TomWhitwell/RadioMusic/Collateral/BuildImages/00.jpg

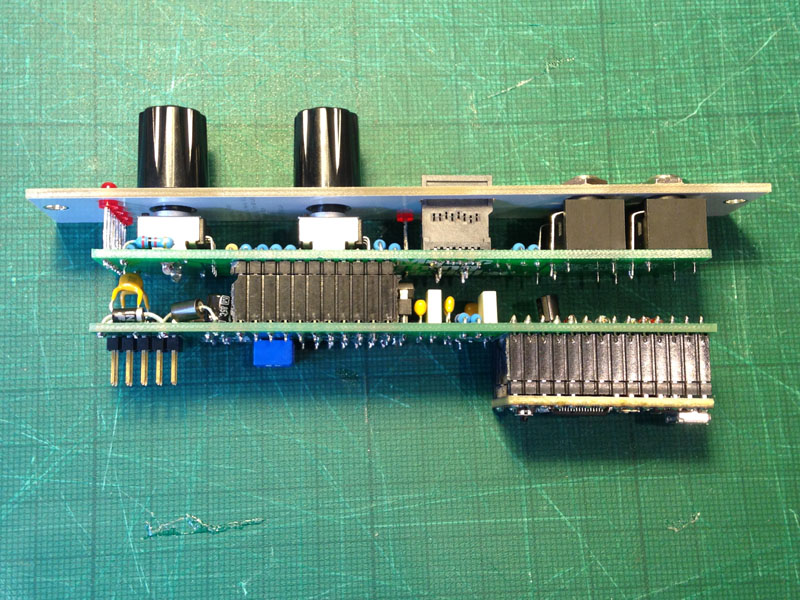
Collateral/BuildImages/00.jpg
