TomWhitwell/RadioMusic/Collateral/BuildImages/01.jpg

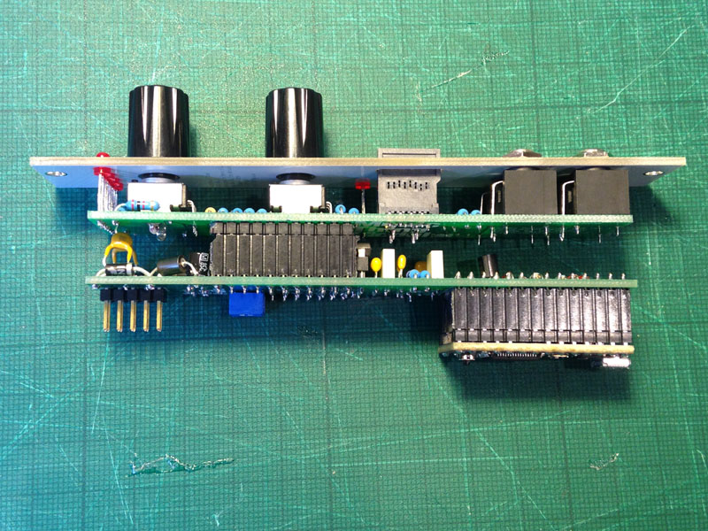
Collateral/BuildImages/01.jpg
