TomWhitwell/RadioMusic/Collateral/BuildImages/02.jpg

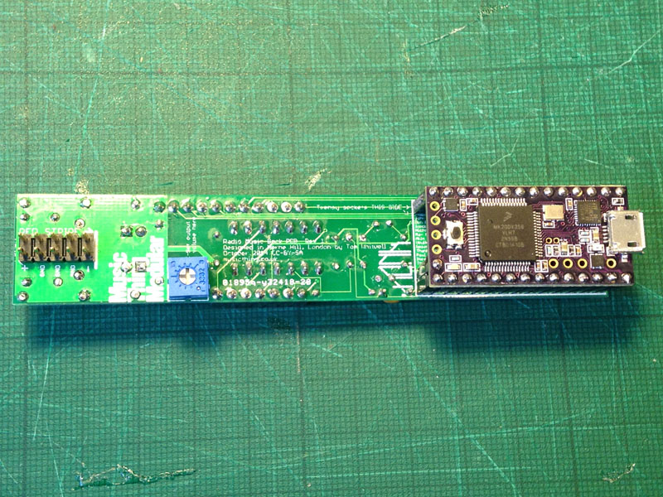
Collateral/BuildImages/02.jpg
