TomWhitwell/RadioMusic/Collateral/BuildImages/03.jpg

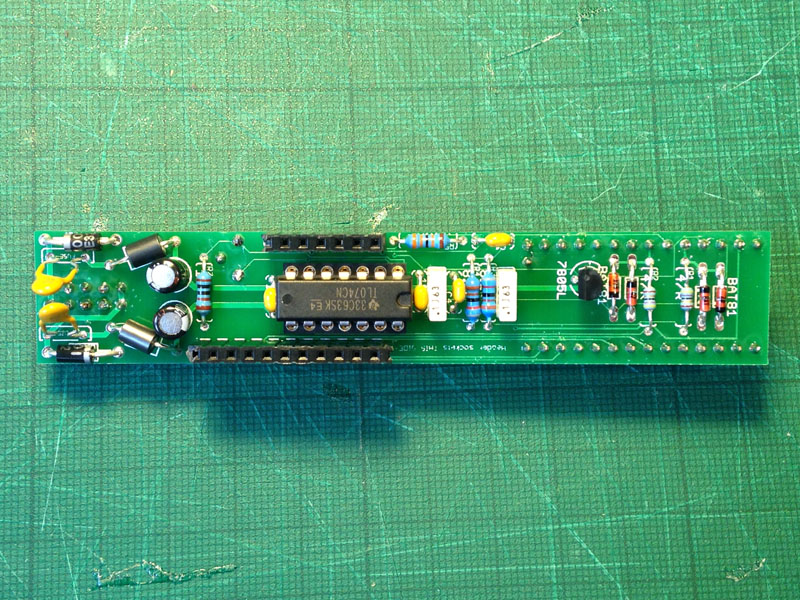
Collateral/BuildImages/03.jpg
