TomWhitwell/RadioMusic/Collateral/BuildImages/04.jpg

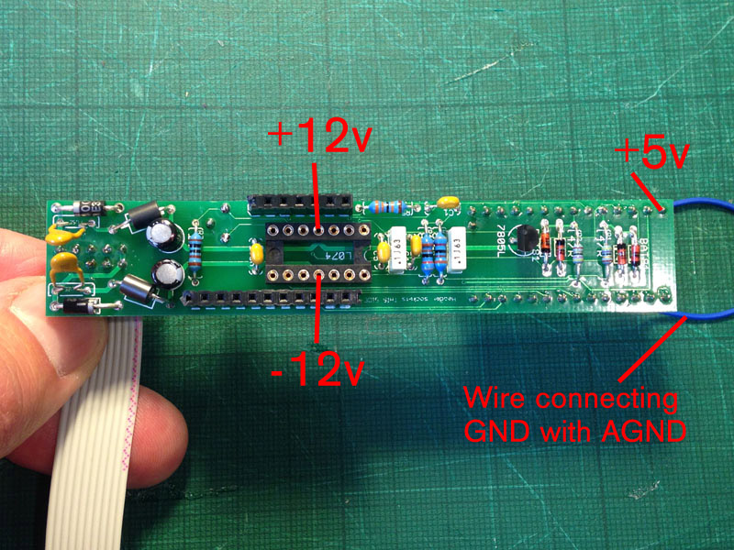
Collateral/BuildImages/04.jpg
