TomWhitwell/RadioMusic/Collateral/BuildImages/05.jpg

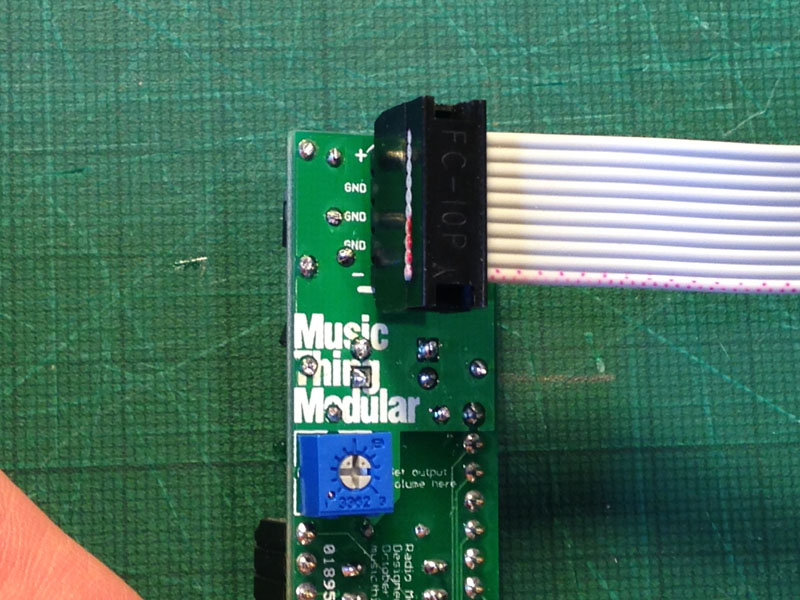
Collateral/BuildImages/05.jpg
