TomWhitwell/RadioMusic/Collateral/BuildImages/06.jpg

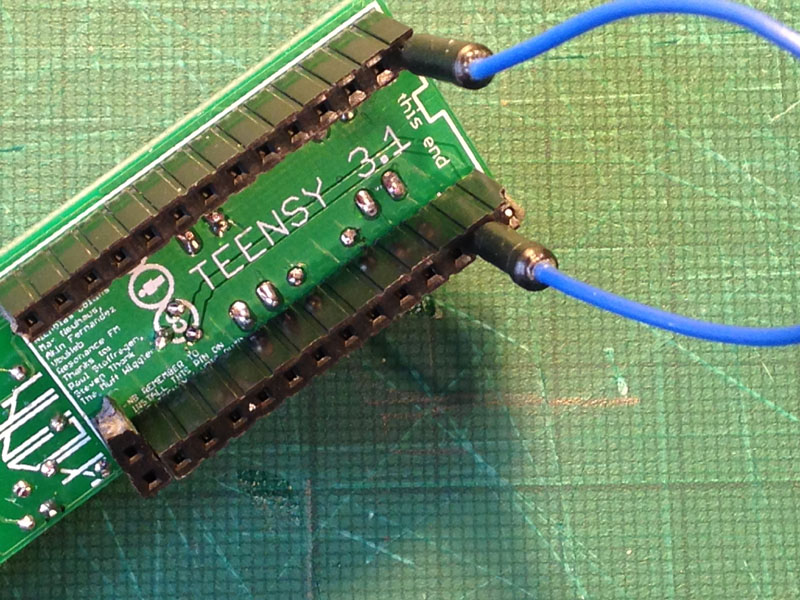
Collateral/BuildImages/06.jpg
