TomWhitwell/RadioMusic/Collateral/BuildImages/07.jpg

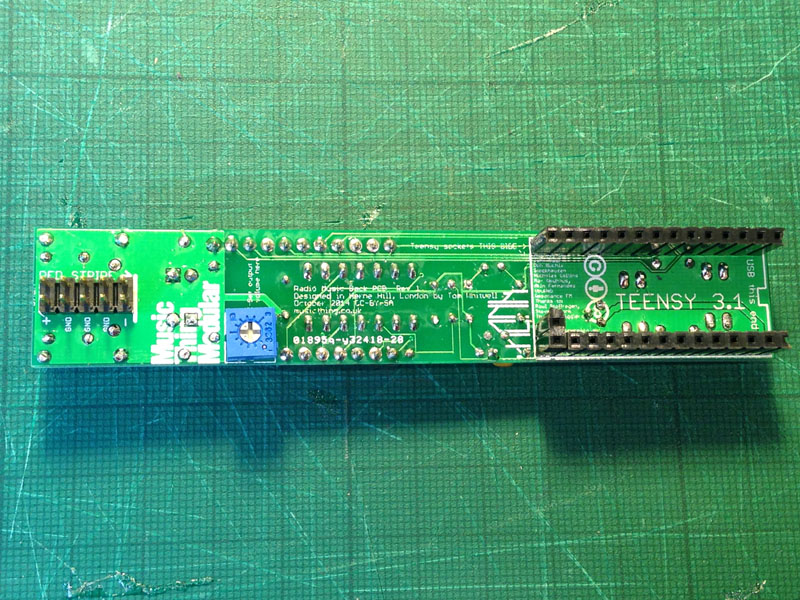
Collateral/BuildImages/07.jpg
