TomWhitwell/RadioMusic/Collateral/BuildImages/09.jpg

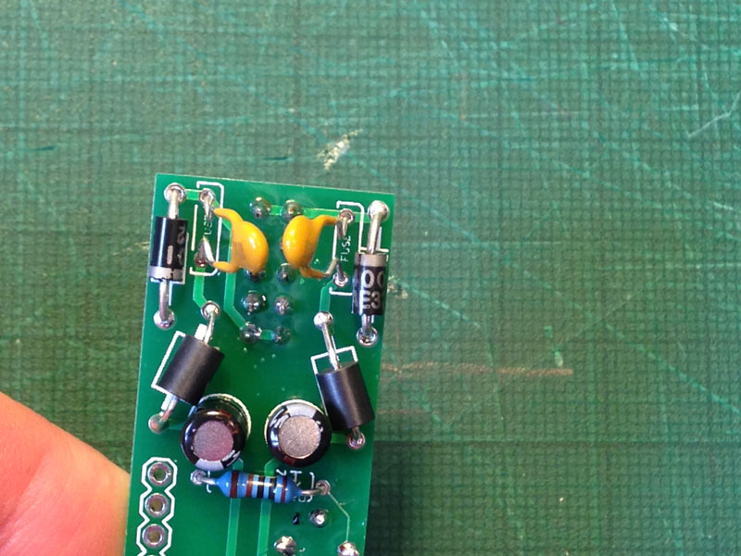
Collateral/BuildImages/09.jpg
