TomWhitwell/RadioMusic/Collateral/BuildImages/10.jpg

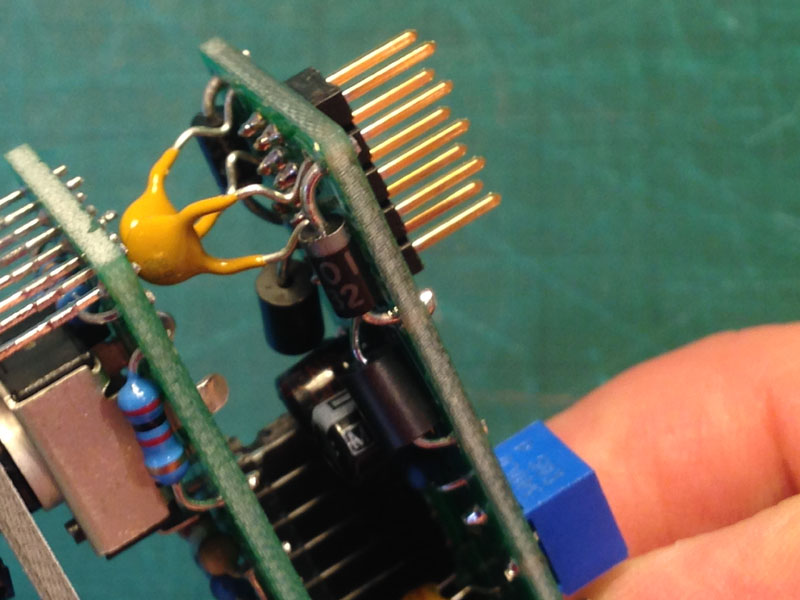
Collateral/BuildImages/10.jpg
