TomWhitwell/RadioMusic/Collateral/BuildImages/11.jpg

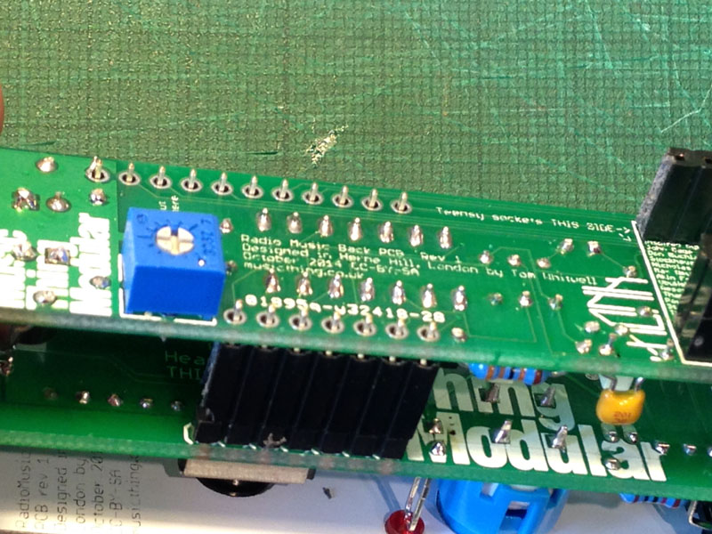
Collateral/BuildImages/11.jpg
