TomWhitwell/RadioMusic/Collateral/BuildImages/12.jpg

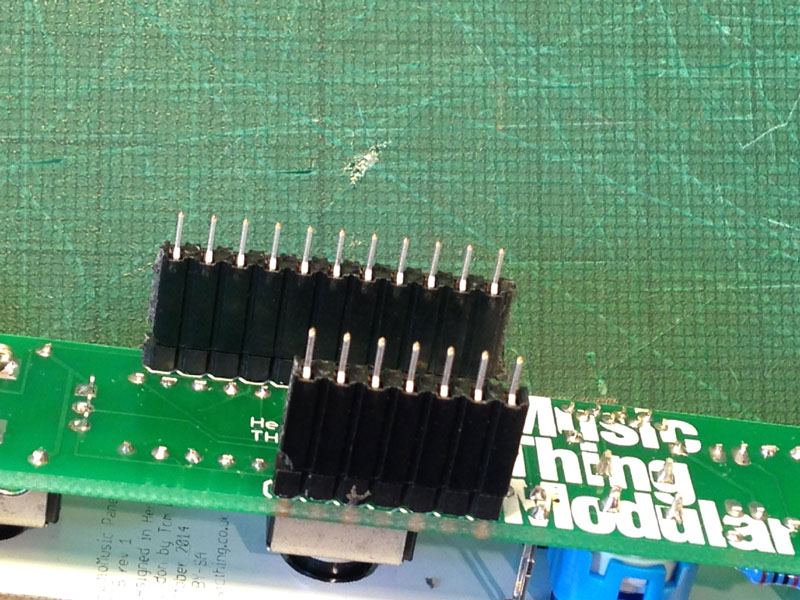
Collateral/BuildImages/12.jpg
