TomWhitwell/RadioMusic/Collateral/BuildImages/13.jpg

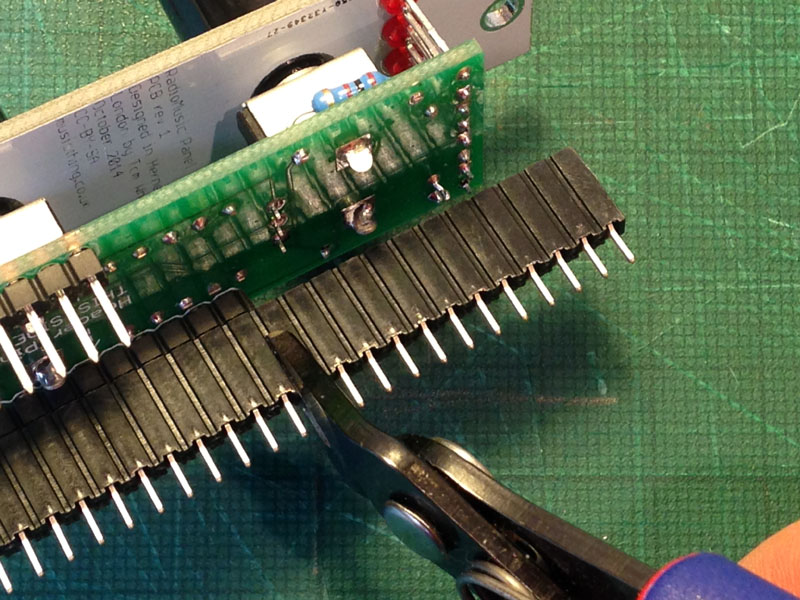
Collateral/BuildImages/13.jpg
