TomWhitwell/RadioMusic/Collateral/BuildImages/14.jpg

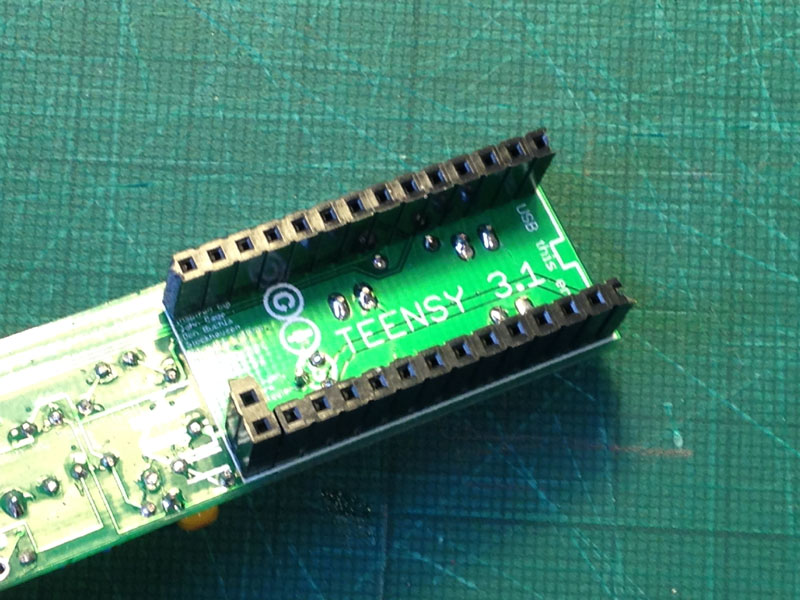
Collateral/BuildImages/14.jpg
