TomWhitwell/RadioMusic/Collateral/BuildImages/16.jpg

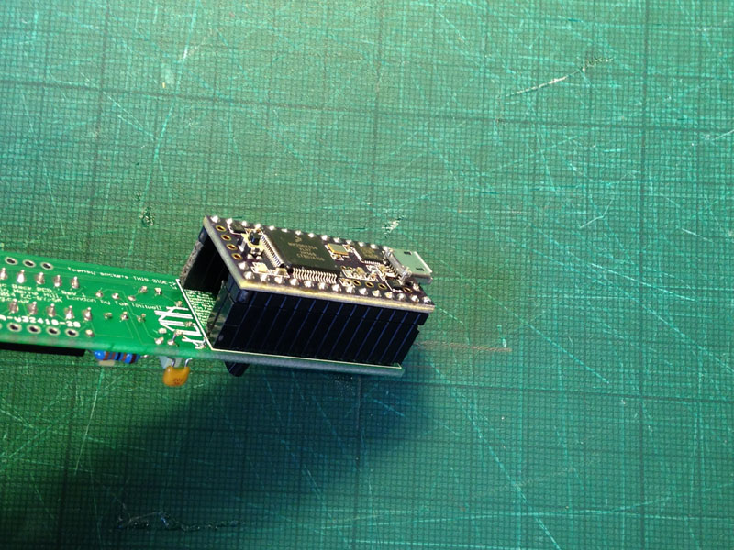
Collateral/BuildImages/16.jpg
