TomWhitwell/RadioMusic/Collateral/BuildImages/17.jpg

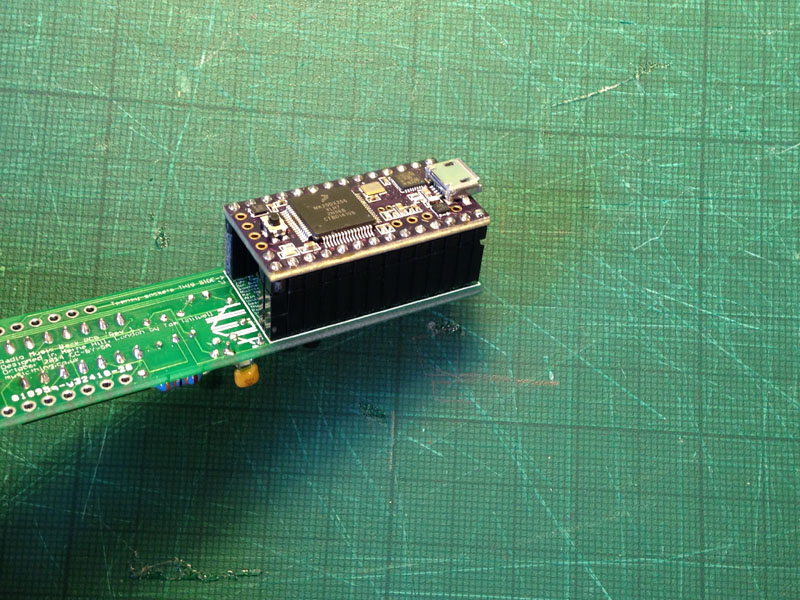
Collateral/BuildImages/17.jpg
