TomWhitwell/RadioMusic/Collateral/BuildImages/18.jpg

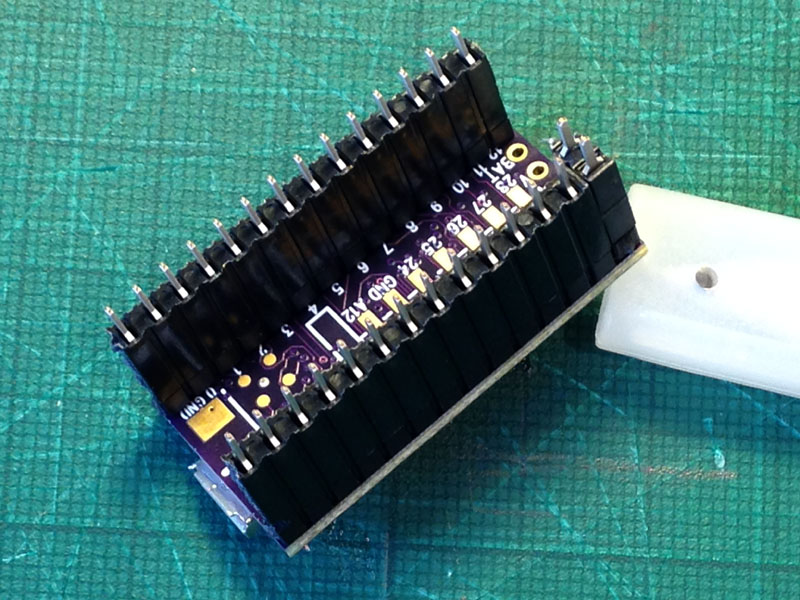
Collateral/BuildImages/18.jpg
