TomWhitwell/RadioMusic/Collateral/BuildImages/19.jpg

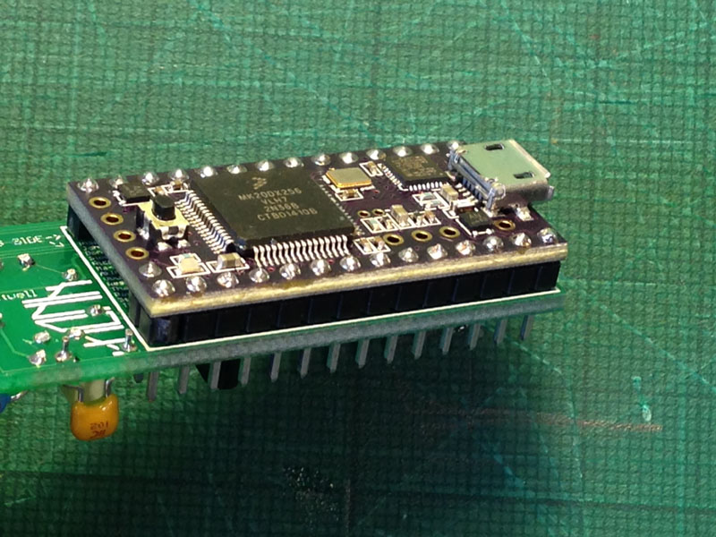
Collateral/BuildImages/19.jpg
