TomWhitwell/RadioMusic/Collateral/BuildImages/20.jpg

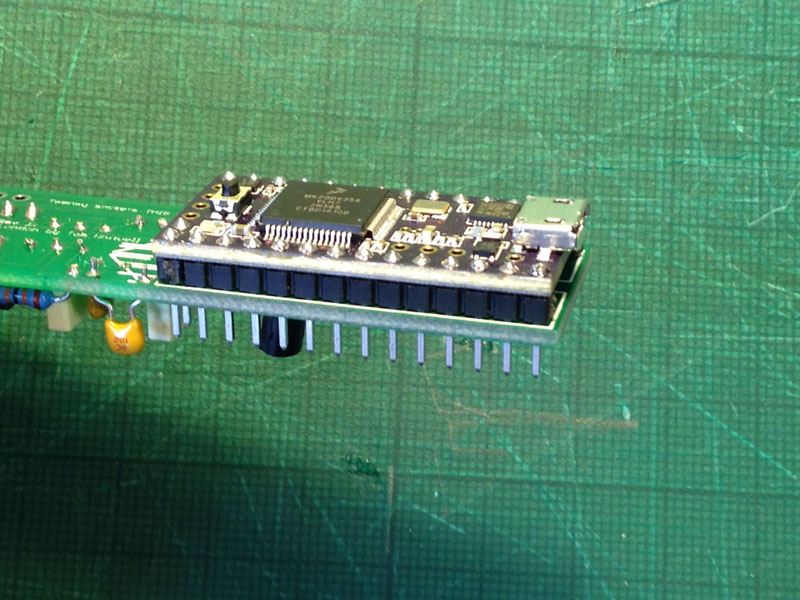
Collateral/BuildImages/20.jpg
