TomWhitwell/RadioMusic/Collateral/BuildImages/21.jpg

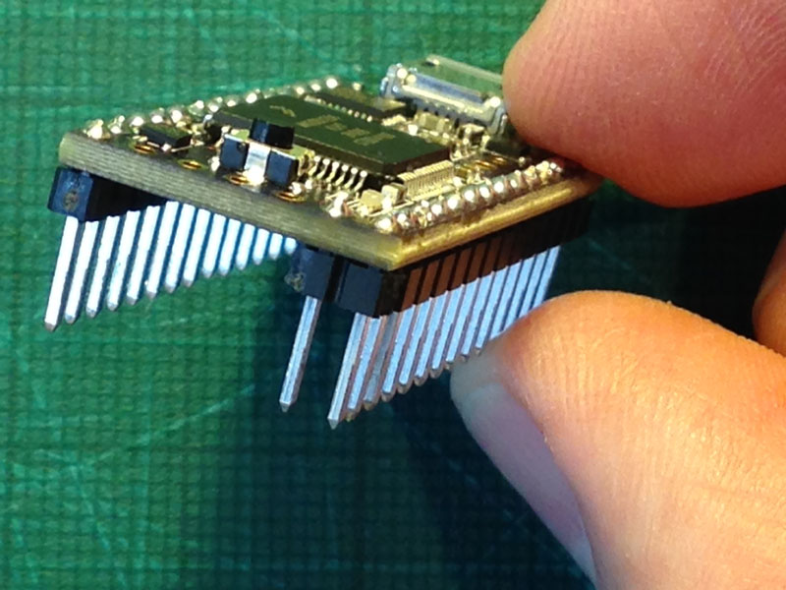
Collateral/BuildImages/21.jpg
