TomWhitwell/RadioMusic/Collateral/BuildImages/22.jpg

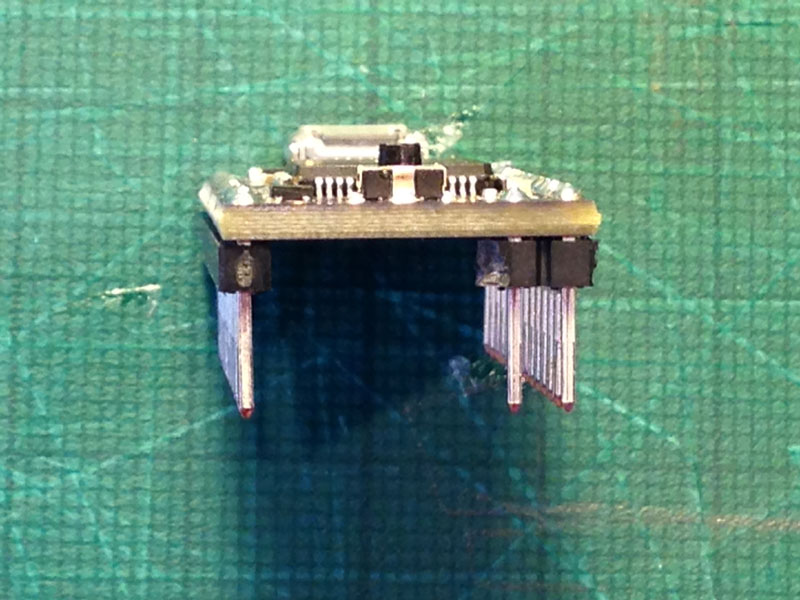
Collateral/BuildImages/22.jpg
