TomWhitwell/RadioMusic/Collateral/BuildImages/23.jpg

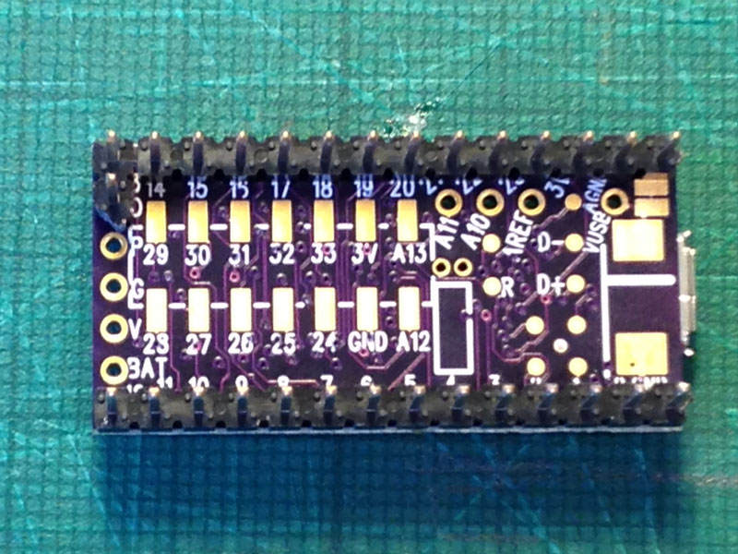
Collateral/BuildImages/23.jpg
