TomWhitwell/RadioMusic/Collateral/BuildImages/24.jpg

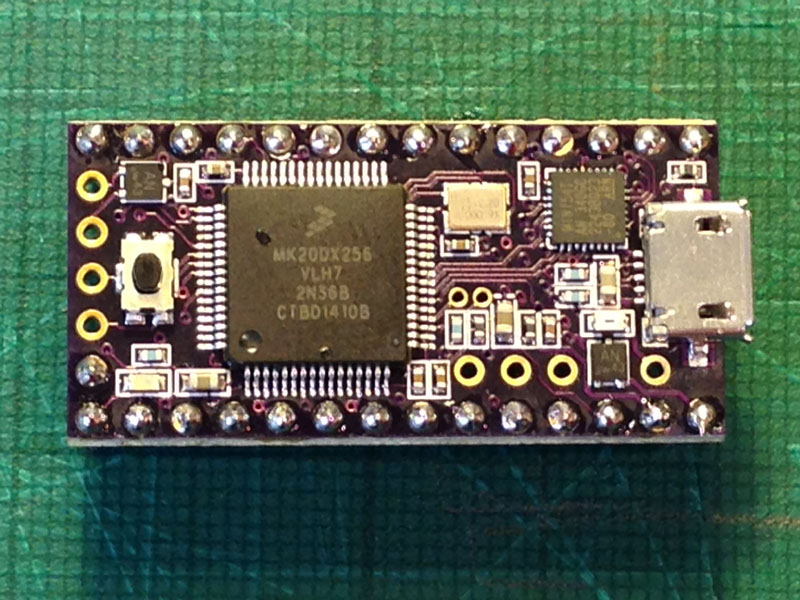
Collateral/BuildImages/24.jpg
