TomWhitwell/RadioMusic/Collateral/BuildImages/25.jpg

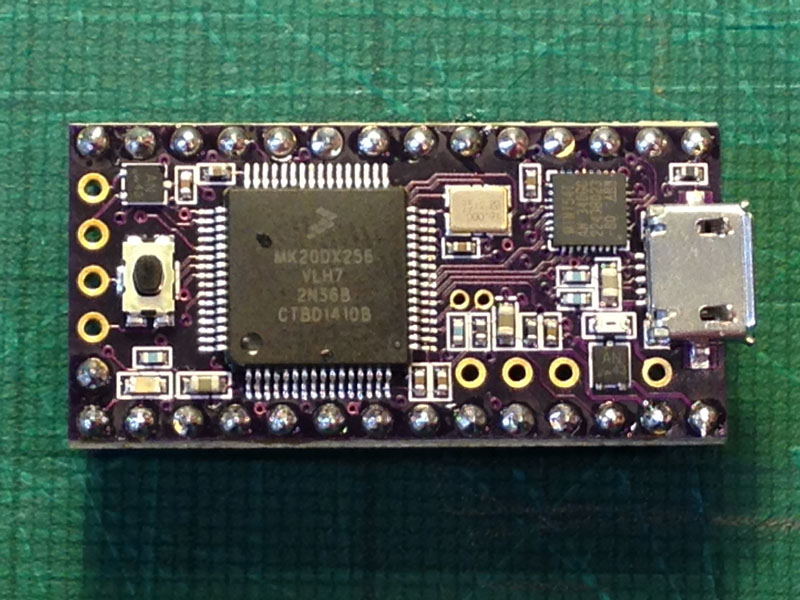
Collateral/BuildImages/25.jpg
