TomWhitwell/RadioMusic/Collateral/BuildImages/26.jpg

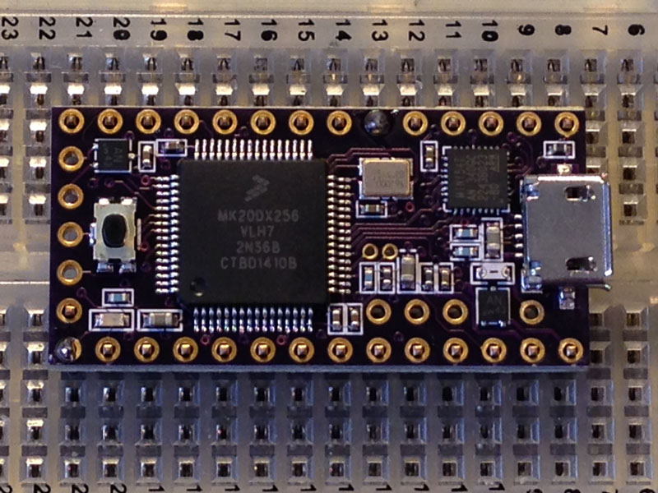
Collateral/BuildImages/26.jpg
