TomWhitwell/RadioMusic/Collateral/BuildImages/27.jpg

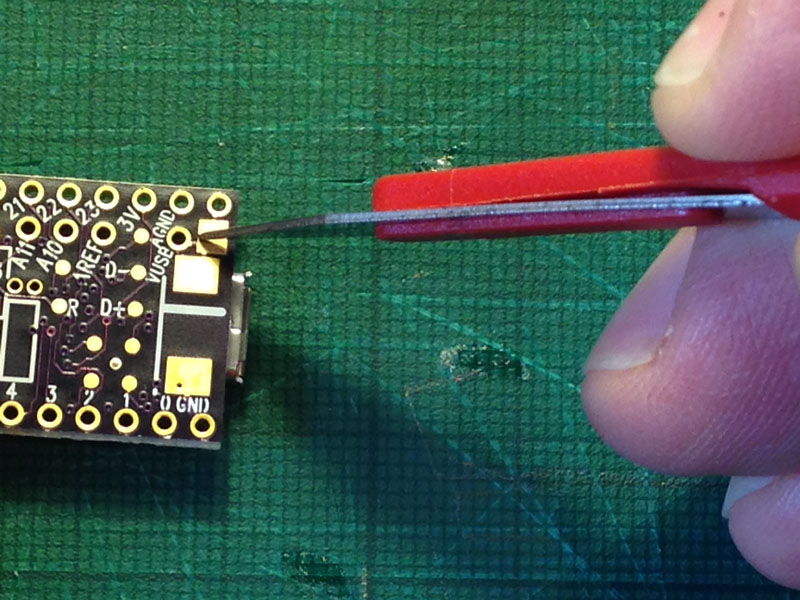
Collateral/BuildImages/27.jpg
