TomWhitwell/RadioMusic/Collateral/BuildImages/28.jpg

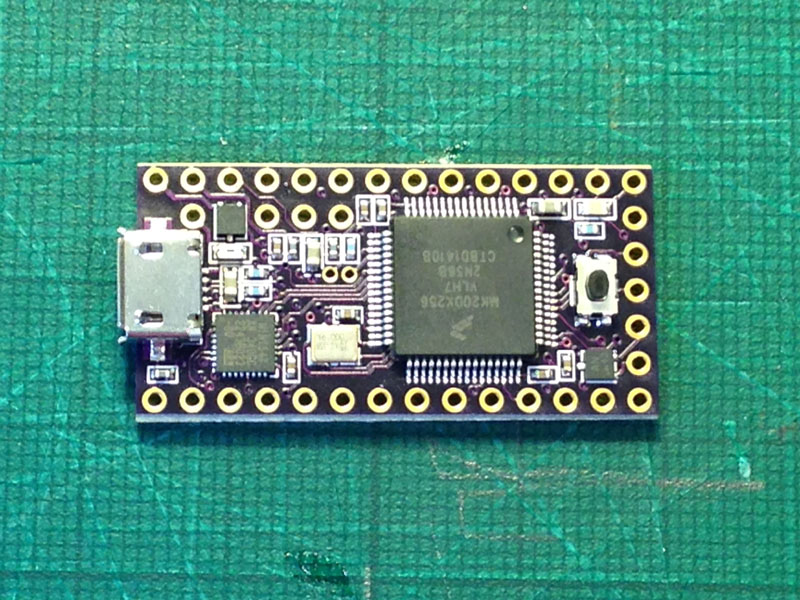
Collateral/BuildImages/28.jpg
