TomWhitwell/RadioMusic/Collateral/BuildImages/29.jpg

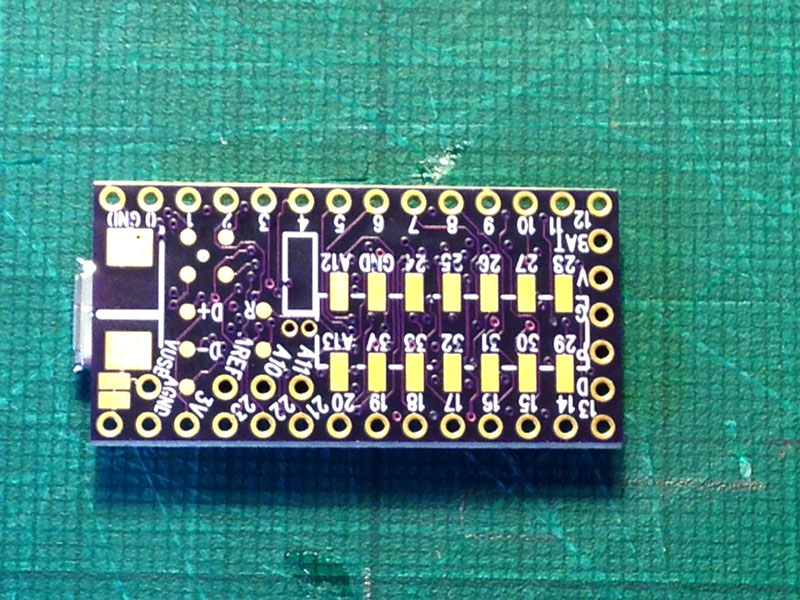
Collateral/BuildImages/29.jpg
