TomWhitwell/RadioMusic/Collateral/BuildImages/30.jpg

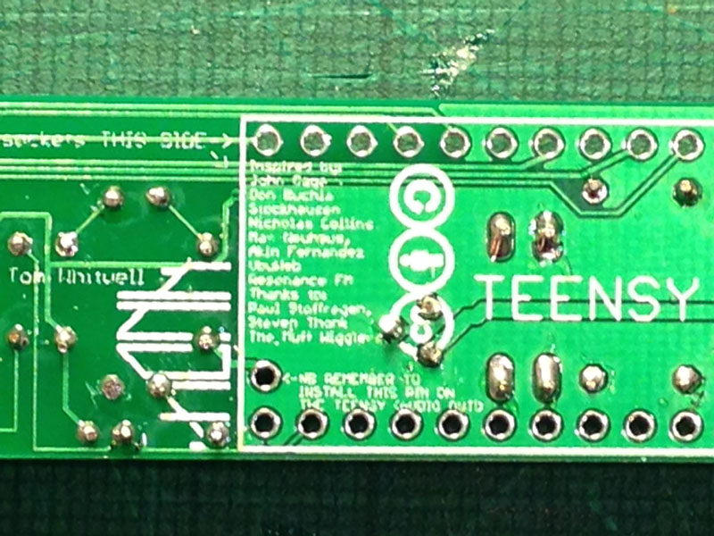
Collateral/BuildImages/30.jpg
