TomWhitwell/RadioMusic/Collateral/BuildImages/31.jpg

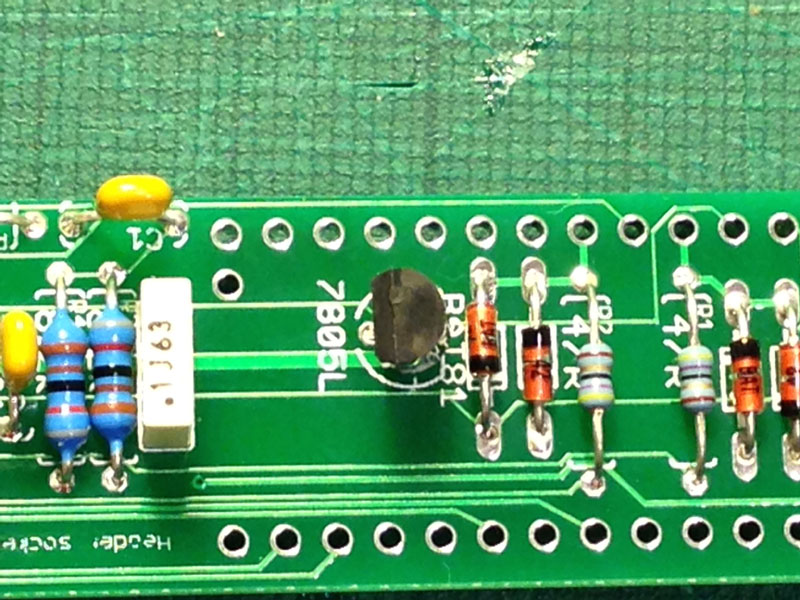
Collateral/BuildImages/31.jpg
