TomWhitwell/RadioMusic/Collateral/BuildImages/32.jpg

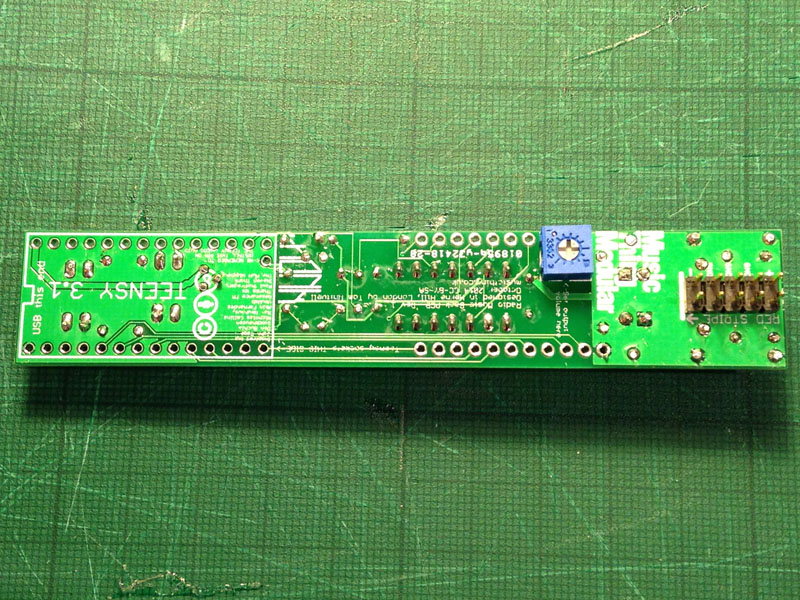
Collateral/BuildImages/32.jpg
