TomWhitwell/RadioMusic/Collateral/BuildImages/33.jpg

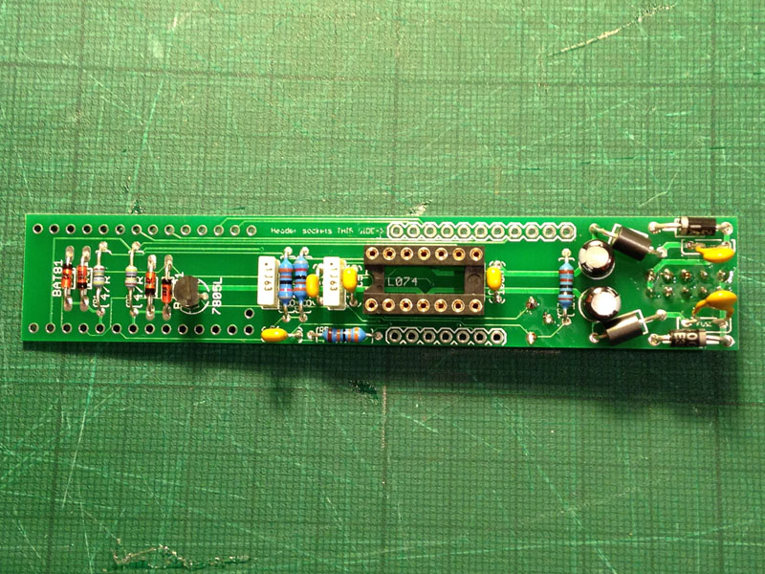
Collateral/BuildImages/33.jpg
