TomWhitwell/RadioMusic/Collateral/BuildImages/34.jpg

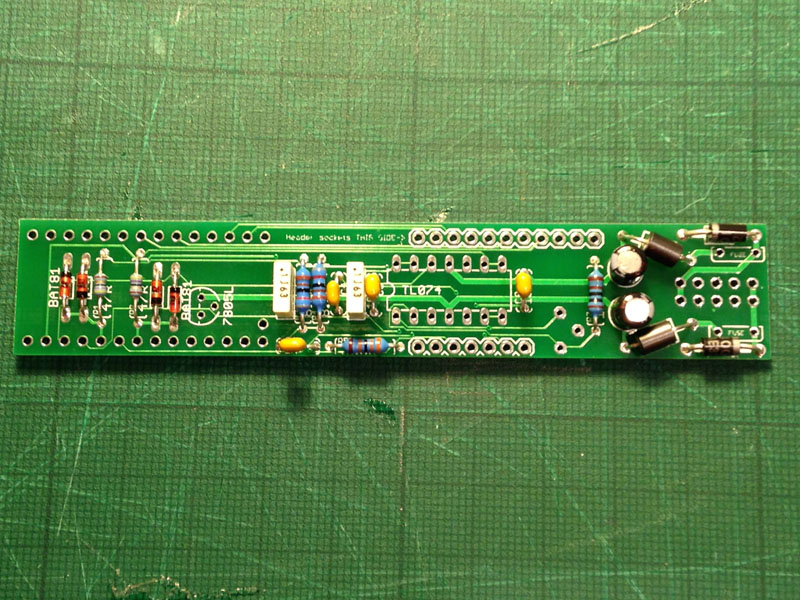
Collateral/BuildImages/34.jpg
