TomWhitwell/RadioMusic/Collateral/BuildImages/35.jpg

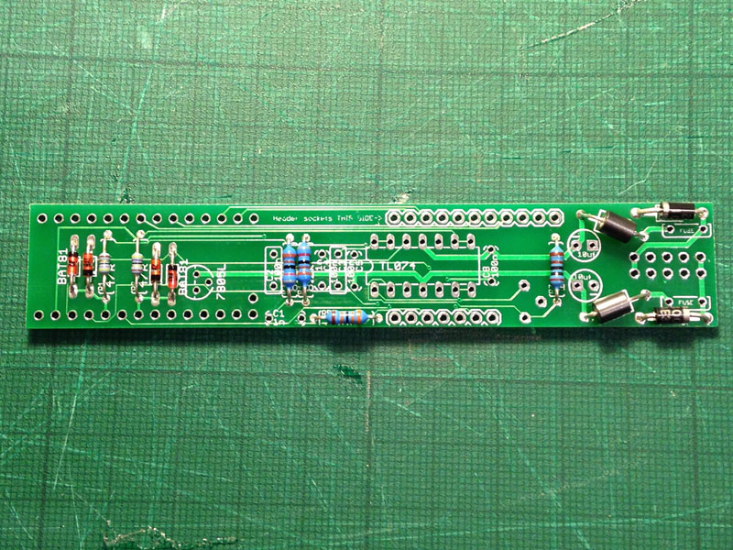
Collateral/BuildImages/35.jpg
