TomWhitwell/RadioMusic/Collateral/BuildImages/36.jpg

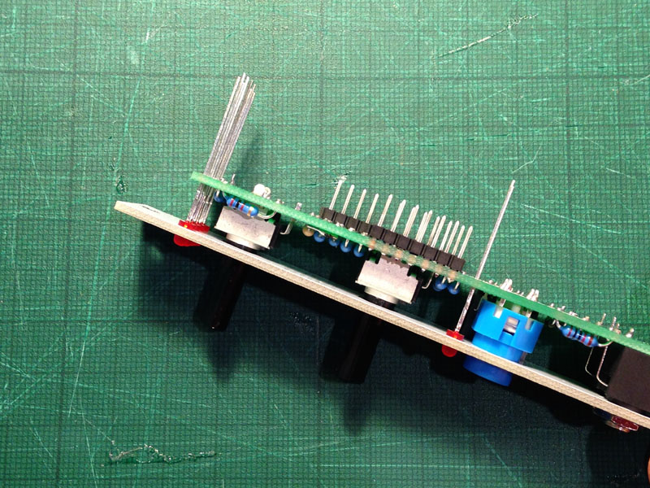
Collateral/BuildImages/36.jpg
