TomWhitwell/RadioMusic/Collateral/BuildImages/37.jpg

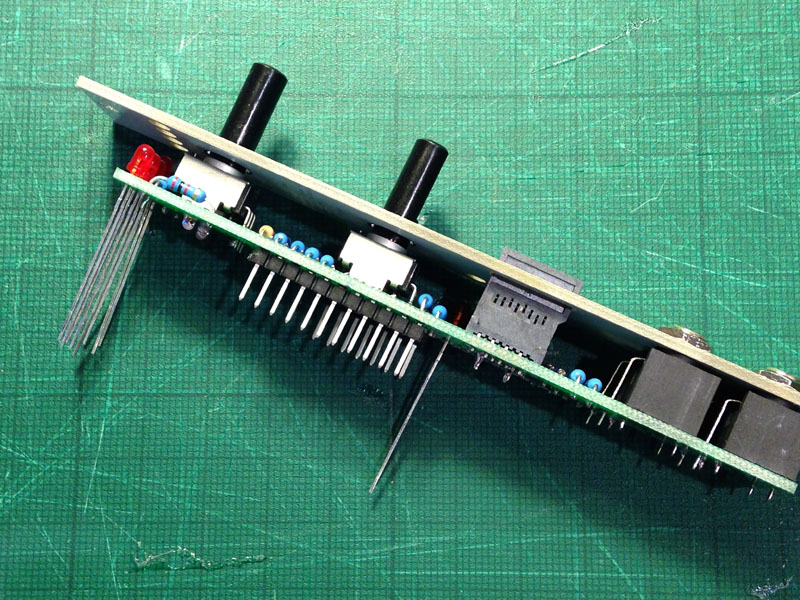
Collateral/BuildImages/37.jpg
