TomWhitwell/RadioMusic/Collateral/BuildImages/38.jpg

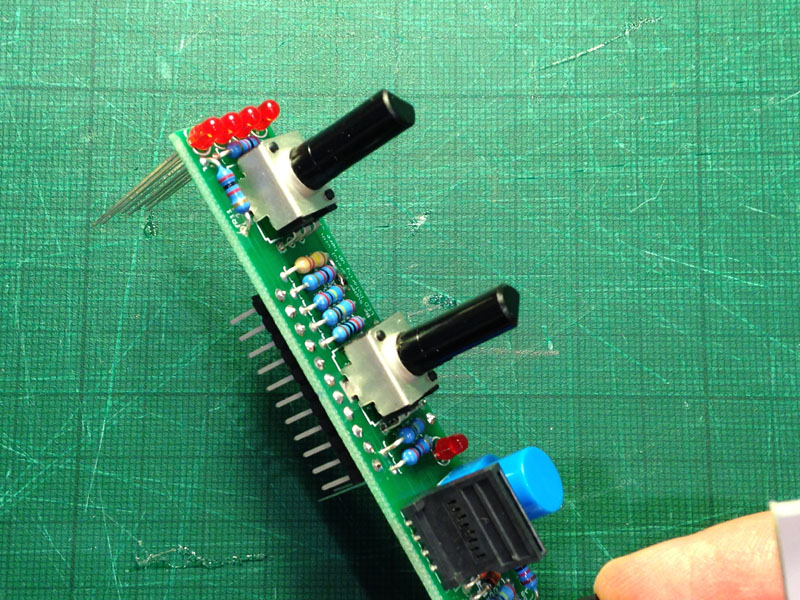
Collateral/BuildImages/38.jpg
