TomWhitwell/RadioMusic/Collateral/BuildImages/39.jpg

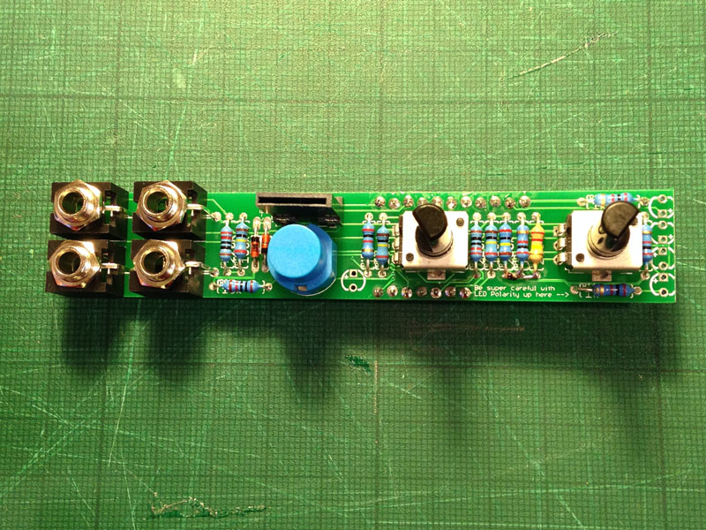
Collateral/BuildImages/39.jpg
