TomWhitwell/RadioMusic/Collateral/BuildImages/40.jpg

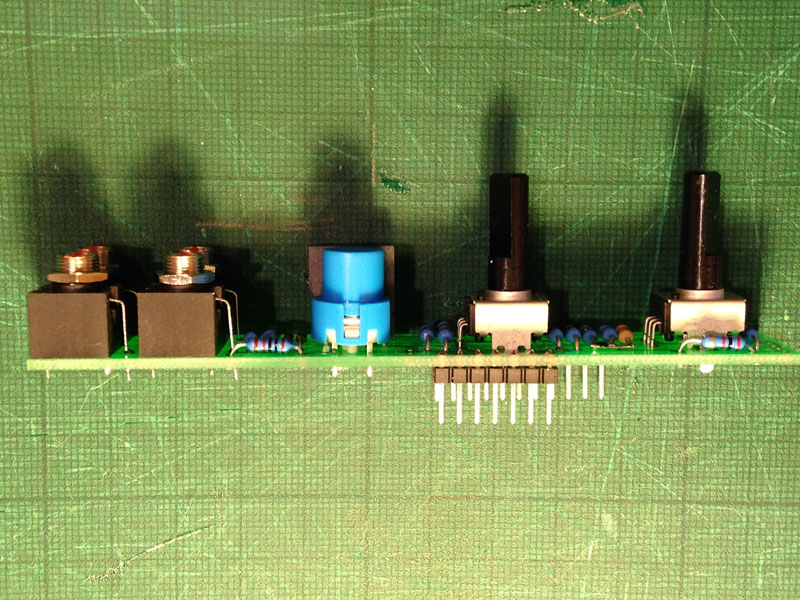
Collateral/BuildImages/40.jpg
