TomWhitwell/RadioMusic/Collateral/BuildImages/42.jpg

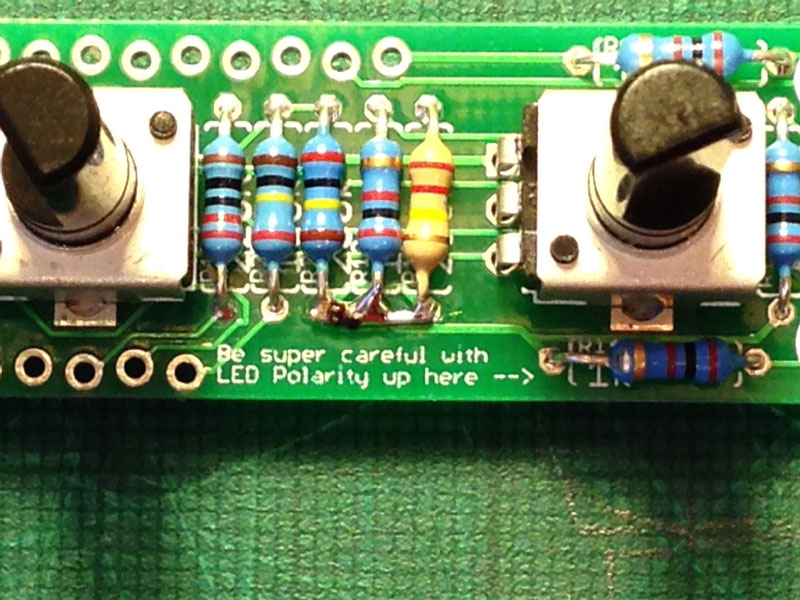
Collateral/BuildImages/42.jpg
