TomWhitwell/RadioMusic/Collateral/BuildImages/43.jpg

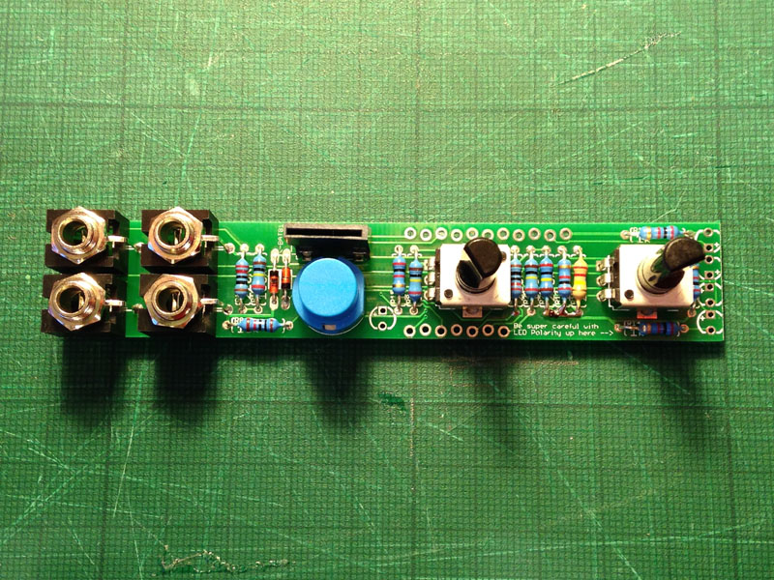
Collateral/BuildImages/43.jpg
