TomWhitwell/RadioMusic/Collateral/BuildImages/44.jpg

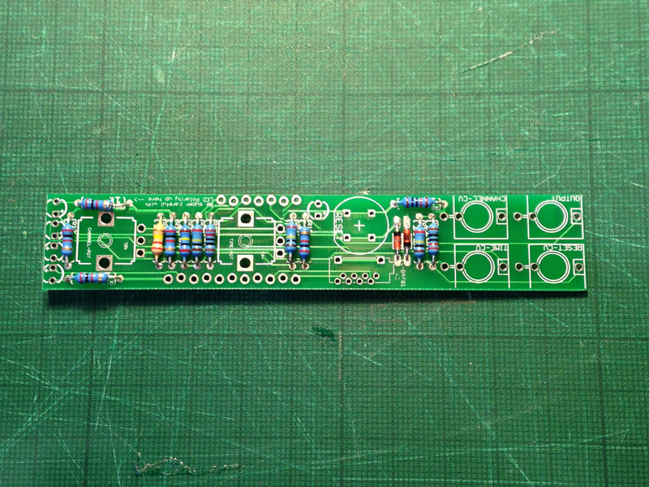
Collateral/BuildImages/44.jpg
