TomWhitwell/RadioMusic/Collateral/BuildImages/45.jpg

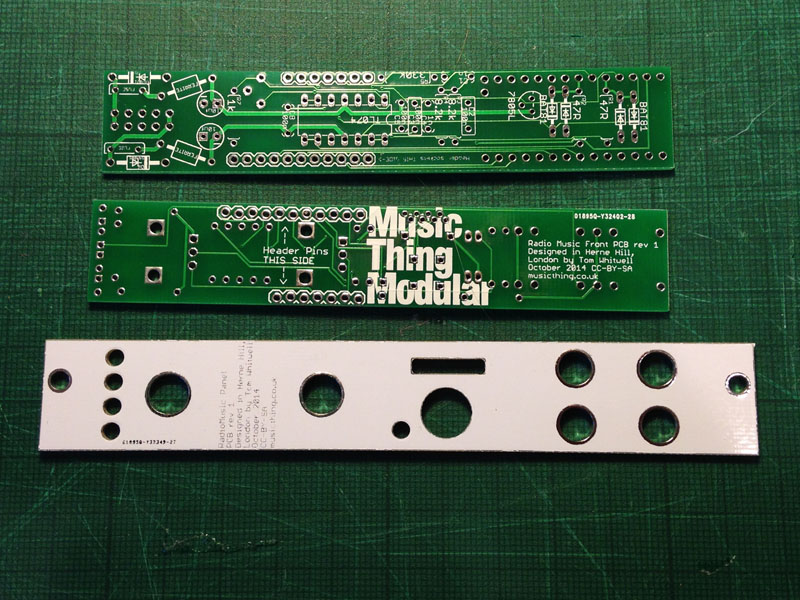
Collateral/BuildImages/45.jpg
