TomWhitwell/RadioMusic/Collateral/BuildImages/46.jpg

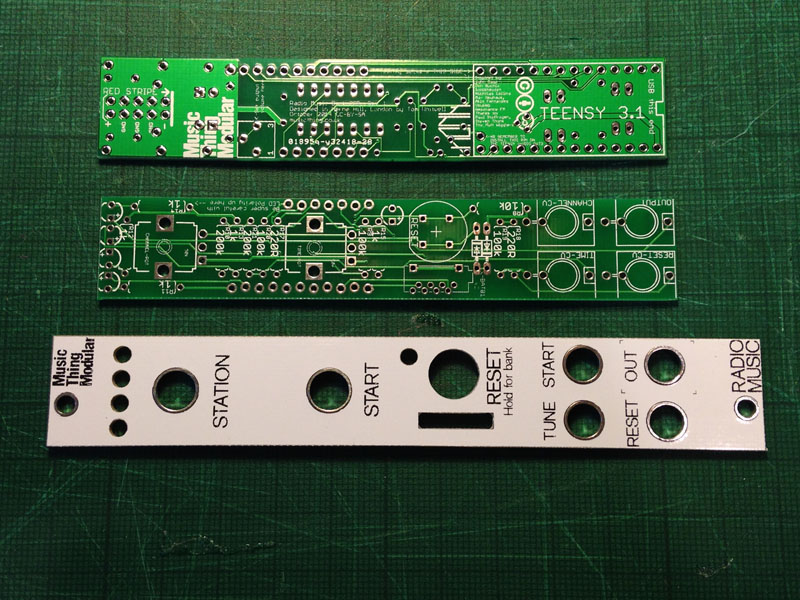
Collateral/BuildImages/46.jpg
