TomWhitwell/RadioMusic/Collateral/BuildImages/47.jpg

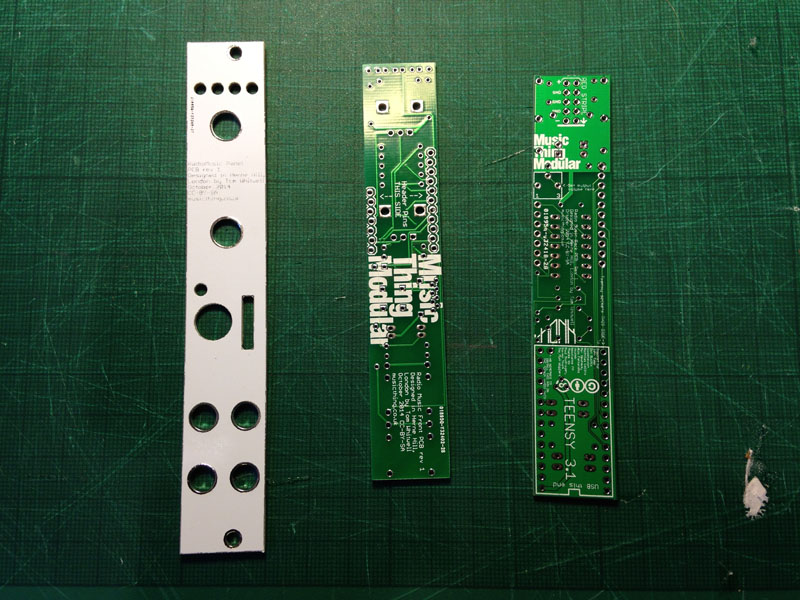
Collateral/BuildImages/47.jpg
