TomWhitwell/RadioMusic/Collateral/BuildImages/48.jpg

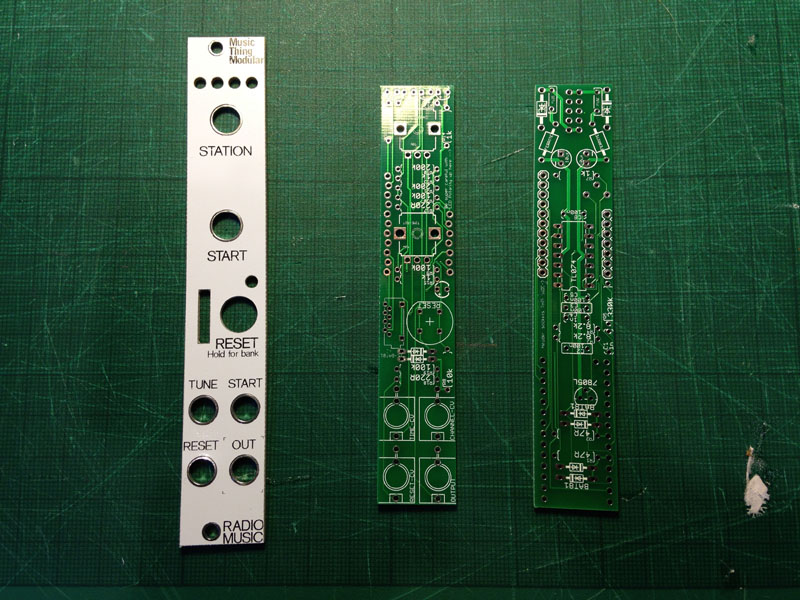
Collateral/BuildImages/48.jpg
