TomWhitwell/RadioMusic/Collateral/BuildImages/49.jpg

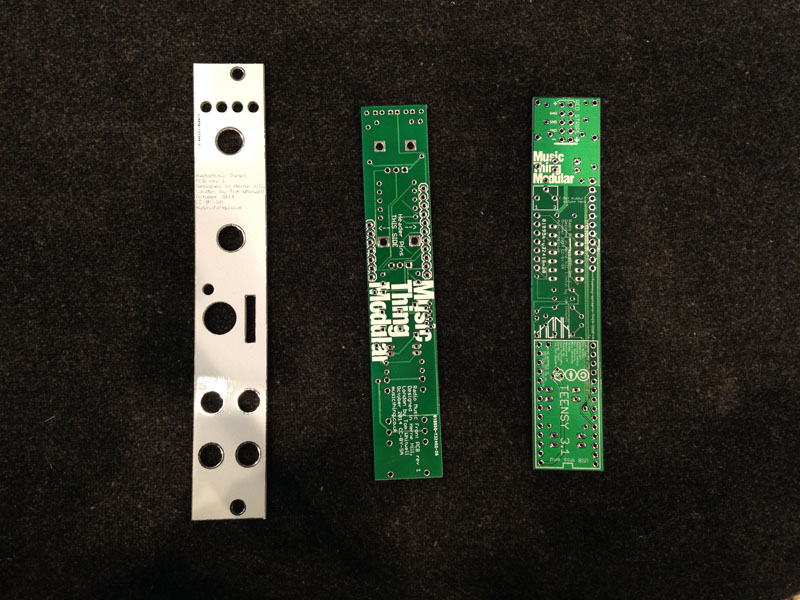
Collateral/BuildImages/49.jpg
