TomWhitwell/RadioMusic/Collateral/BuildImages/button.jpg

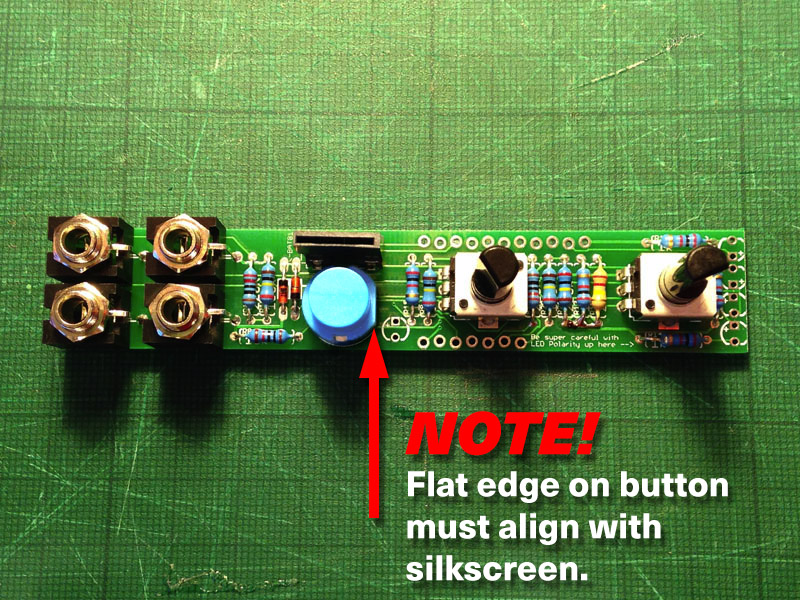
Collateral/BuildImages/button.jpg
