TomWhitwell/RadioMusic/Collateral/BuildImages/pitchshift.png

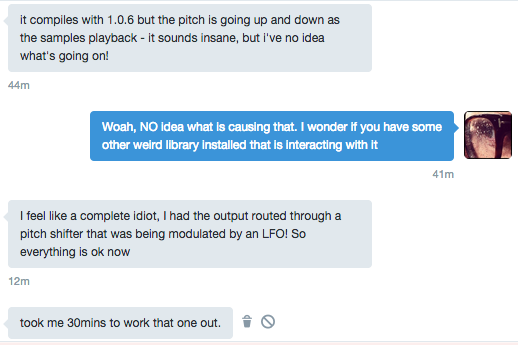
Collateral/BuildImages/pitchshift.png
