TomWhitwell/RadioMusic/Collateral/BuildImages/rawbutton.png

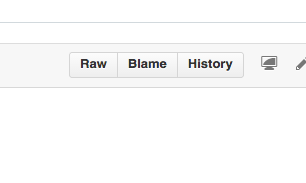
Collateral/BuildImages/rawbutton.png
