TomWhitwell/RadioMusic/Collateral/BuildImages/resistorfix.png

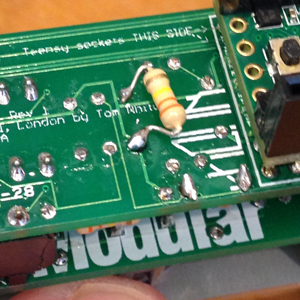
Collateral/BuildImages/resistorfix.png
