TomWhitwell/RadioMusic/RadioMusic/AudioSystemHelpers.h

#ifndef AudioSystemHelpers_h
#define AudioSystemHelpers_h

#include <Audio.h>
#include "RamMonitor.h"

// REBOOT CODES
#define RESTART_ADDR       0xE000ED0C
#define READ_RESTART()     (*(volatile uint32_t *)RESTART_ADDR)
#define WRITE_RESTART(val) ((*(volatile uint32_t *)RESTART_ADDR) = (val))

void reBoot(int delayTime) {
	Serial.println("Rebooting");
//	Serial.end();
	if (delayTime > 0)
		delay(delayTime);
	WRITE_RESTART(0x5FA0004);
}

RamMonitor ramMonitor;
elapsedMillis cpuCheckTimer;

void checkCPU() {
    if (cpuCheckTimer > 3000) {
    	int maxCPU = AudioProcessorUsageMax();

    	Serial.print("MaxCPU : ");
    	Serial.print(maxCPU);
    	Serial.print("\tUnallocated : ");
    	Serial.print(ramMonitor.unallocated());
    	Serial.print("\tFree : ");
    	Serial.println(ramMonitor.free());

    	if(ramMonitor.warning_crash()) {
    		Serial.println("!!!!#### CRASH WARNING #####!!!!");
    	}

    	if(ramMonitor.warning_lowmem()) {
    		Serial.println("!!!!#### LOW MEMORY WARNING #####!!!!");
    	}

    	cpuCheckTimer = 0;
    	AudioProcessorUsageMaxReset();
    }
}

#endif
